BhavyaPatel0306/mosfet-amplifier/simulations/results/baseline-transient.csv

time_s | vout_v | follower_id_a
0.0799 | -0.2110576397 | 7.402031756e-05
0.07990005 | -0.26345121 | 6.402180623e-05
0.0799001 | -0.3151215127 | 5.417157222e-05
0.07990015 | -0.3667388929 | 4.433218787e-05
0.0799002 | -0.4183562731 | 3.449280352e-05
0.07990025 | -0.4699736533 | 2.465341917e-05
0.0799003 | -0.509584981 | 1.739860275e-05
0.07990035 | -0.5483178095 | 1.033290269e-05
0.0799004 | -0.587050638 | 3.267202628e-06
0.07990045 | -0.598102574 | 1.722875323e-06
0.0799005 | -0.6074028379 | 5.279455032e-07
0.07990055 | -0.6104110611 | 1.505764021e-08
0.0799006 | -0.6088211872 | 5.923497455e-10
0.07990065 | -0.6100654802 | 1.226483665e-10
0.0799007 | -0.6096421933 | 5.598703837e-11
0.07990075 | -0.6097869455 | 3.33456932e-11
0.0799008 | -0.6097448757 | 2.368956704e-11
0.07990085 | -0.609761513 | 1.800128566e-11
0.0799009 | -0.6097532343 | 1.50065299e-11
0.07990095 | -0.609745538 | 1.214112063e-11
0.079901 | -0.6097474793 | 1.061282643e-11
0.07990105 | -0.6097494205 | 9.084532233e-12
0.0799011 | -0.6097468562 | 8.159850005e-12
0.07990115 | -0.6097433783 | 7.357538007e-12
0.0799012 | -0.6097399005 | 6.55522601e-12
0.07990125 | -0.6097384936 | 6.016057738e-12
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
