BhavyaPatel0306/mosfet-amplifier/simulations/results/candidate-ac-loaded.csv

frequency_hz | vout_real_v | vout_imag_v
1 | -0.6750733711 | -0.1610473698
1.011579454 | -0.7141217064 | -0.1595094952
1.023292992 | -0.7552116015 | -0.1571780903
1.035142167 | -0.798431141 | -0.1539674079
1.047128548 | -0.8438705795 | -0.1497850583
1.059253725 | -0.8916222372 | -0.1445316126
1.071519305 | -0.9417803752 | -0.1381001918
1.083926914 | -0.9944410496 | -0.130376039
1.096478196 | -1.049701942 | -0.1212360782
1.109174815 | -1.107662164 | -0.1105484573
1.122018454 | -1.168422036 | -0.0981720773
1.135010816 | -1.232082832 | -0.08395610791
1.148153621 | -1.298746501 | -0.06773948994
1.161448614 | -1.368515349 | -0.04935042576
1.174897555 | -1.441491686 | -0.02860585856
1.188502227 | -1.517777437 | -0.005310941679
1.202264435 | -1.597473713 | 0.02074150075
1.216186001 | -1.680680339 | 0.04977152016
1.230268771 | -1.767495334 | 0.08201259539
1.244514612 | -1.858014351 | 0.1177121878
1.258925412 | -1.952330063 | 0.1571322981
1.273503081 | -2.050531499 | 0.200550021
1.288249552 | -2.152703322 | 0.2482580979
1.303166778 | -2.258925057 | 0.3005654609
1.318256739 | -2.369270258 | 0.3577977687
1.333521432 | -2.483805614 | 0.420297928
1.348962883 | -2.60258999 | 0.4884265994
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
