BhavyaPatel0306/mosfet-amplifier/simulations/results/candidate-ac-unloaded.csv

frequency_hz | vout_real_v | vout_imag_v
1 | -3.280633044 | 10.57293845
1.011579454 | -3.26859896 | 11.06594459
1.023292992 | -3.247282574 | 11.57888967
1.035142167 | -3.215869603 | 12.11235414
1.047128548 | -3.173497963 | 12.6669179
1.059253725 | -3.119255929 | 13.24315866
1.071519305 | -3.052180309 | 13.84165015
1.083926914 | -2.971254611 | 14.46296005
1.096478196 | -2.875407219 | 15.10764794
1.109174815 | -2.763509598 | 15.77626297
1.122018454 | -2.63437452 | 16.46934141
1.135010816 | -2.486754327 | 17.18740402
1.148153621 | -2.319339243 | 17.93095321
1.161448614 | -2.130755748 | 18.70047008
1.174897555 | -1.919565012 | 19.49641124
1.188502227 | -1.684261426 | 20.31920541
1.202264435 | -1.423271211 | 21.16924986
1.216186001 | -1.134951152 | 22.04690666
1.230268771 | -0.8175874423 | 22.95249871
1.244514612 | -0.4693946797 | 23.88630557
1.258925412 | -0.08851500619 | 24.84855908
1.273503081 | 0.3269825735 | 25.83943883
1.288249552 | 0.7791026865 | 26.85906735
1.303166778 | 1.26992388 | 27.90750516
1.318256739 | 1.801598681 | 28.98474564
1.333521432 | 2.376353416 | 30.09070961
1.348962883 | 2.996487762 | 31.22523989
1.364583137 | 3.664374016 | 32.38809552
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
